majabojarska/sculptr-delta-mk1/Thingiverse/files/LCD_front.stl

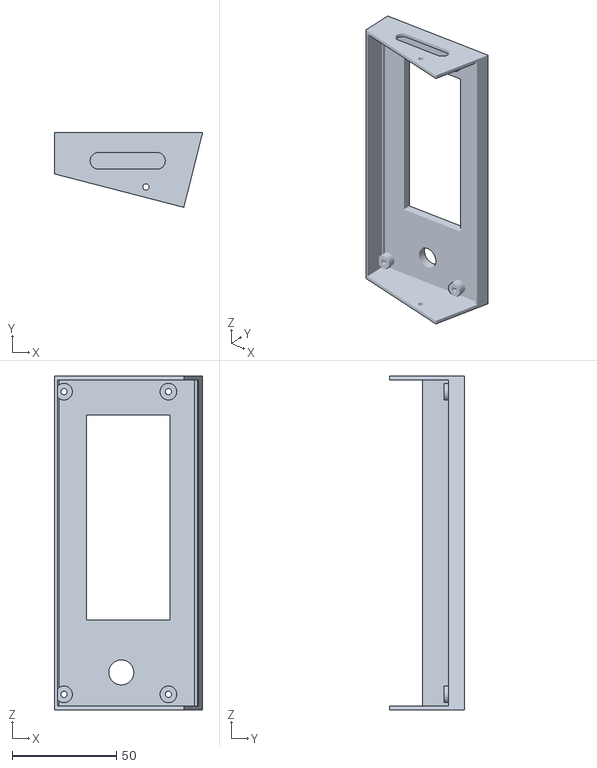
[picture p18: CAD file, 2019-02-17, an earlier design]
Thingiverse/files/LCD_front.stl
71.0 x 35.8 x 160.0
