majabojarska/sculptr-delta-mk1/Thingiverse/files/foot.stl

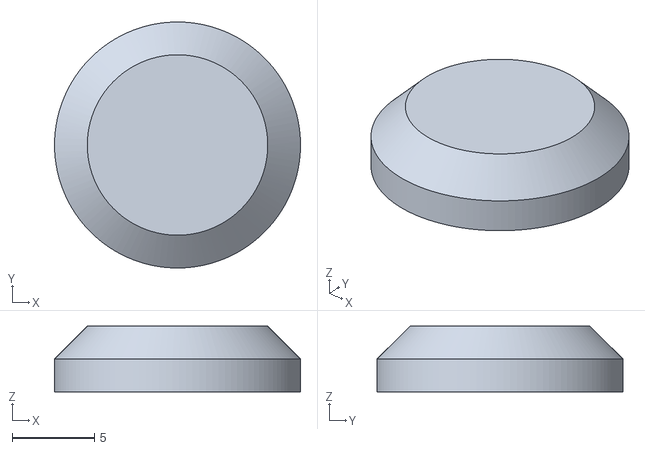
[picture p19: CAD file, 2019-02-17, an earlier design]
Thingiverse/files/foot.stl
15.0 x 15.0 x 4.00
