majabojarska/sculptr-delta-mk1/Thingiverse/files/LCD_front_rods_support.stl

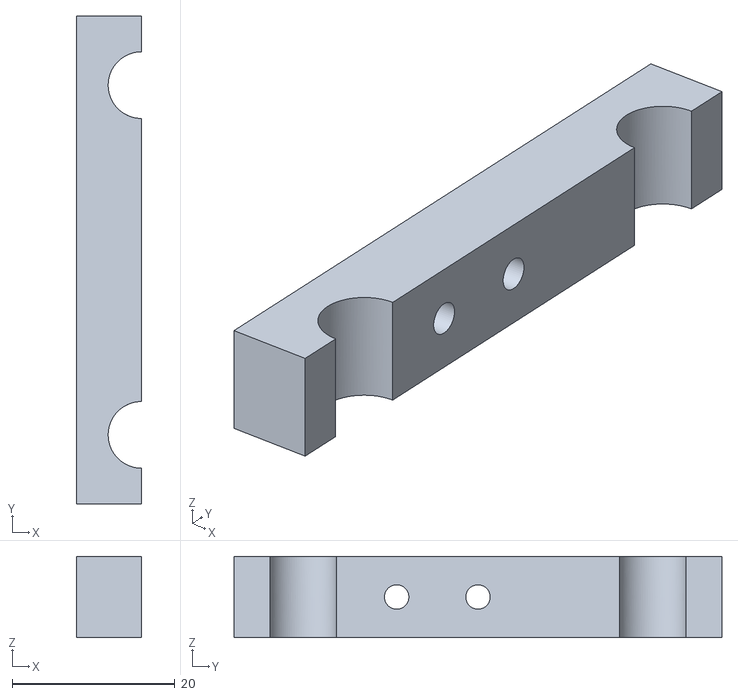
[picture p20: CAD file, 2019-02-17, an earlier design]
Thingiverse/files/LCD_front_rods_support.stl
8.00 x 60.0 x 10.0
